nikhilmishra000/robot_arm/sw/gripper/finger2.SLDPRT

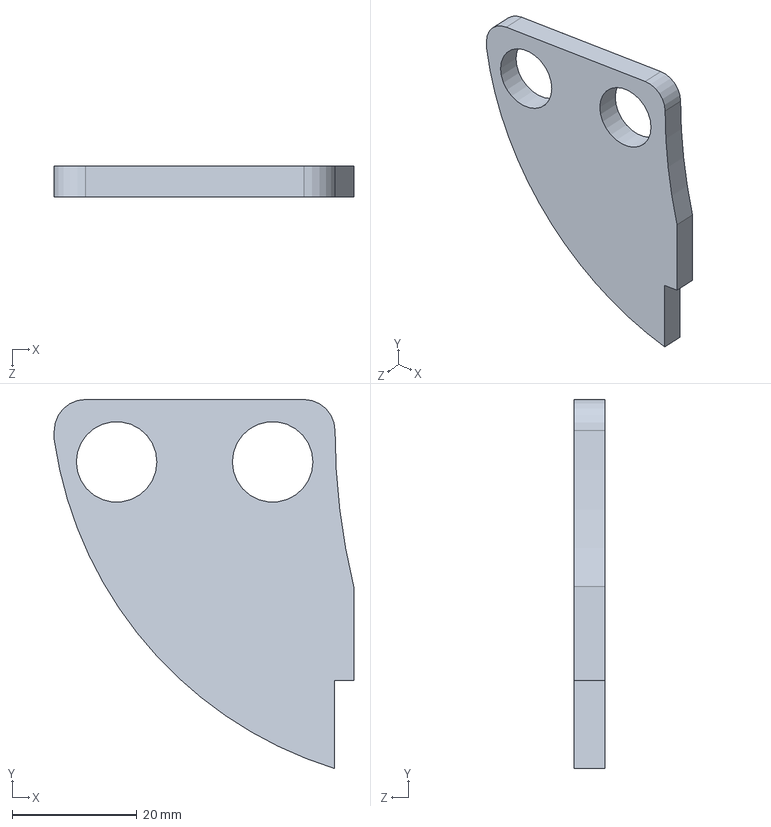
[picture p15: CAD file, 2015-05-30]
sw/gripper/finger2.SLDPRT
48.0 x 59.1 x 5.00 mm
