nikhilmishra000/robot_arm/sw/shoulder/shoulder5.SLDPRT

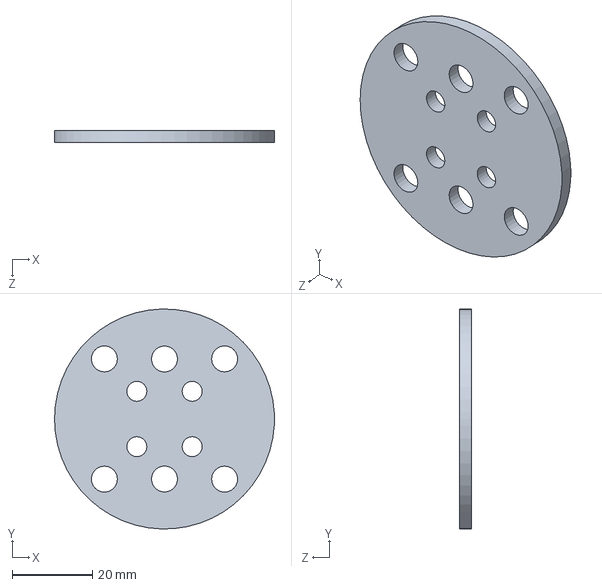
[picture p16: CAD file, 2015-05-30]
sw/shoulder/shoulder5.SLDPRT
55.0 x 55.0 x 3.10 mm
