nikhilmishra000/robot_arm/sw/upper_arm/upper_arm4.SLDPRT

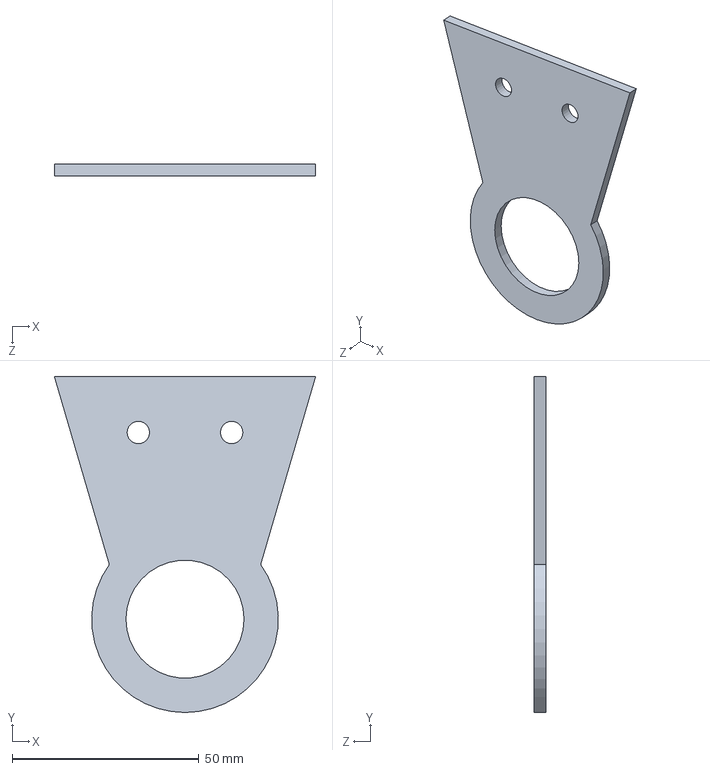
[picture p17: CAD file, 2015-05-30]
sw/upper_arm/upper_arm4.SLDPRT
70.0 x 90.0 x 3.10 mm
