nikhilmishra000/robot_arm/sw/wrist/wrist2_(1,2).SLDPRT

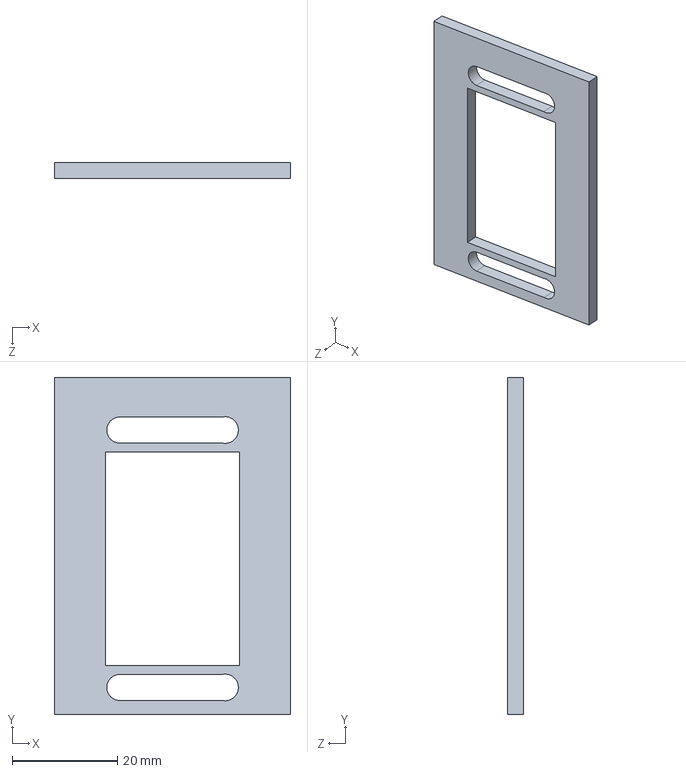
[picture p18: CAD file, 2015-05-30]
sw/wrist/wrist2_(1,2).SLDPRT
45.0 x 64.2 x 3.10 mm
