nikhilmishra000/robot_arm/sw/base/base2.SLDPRT

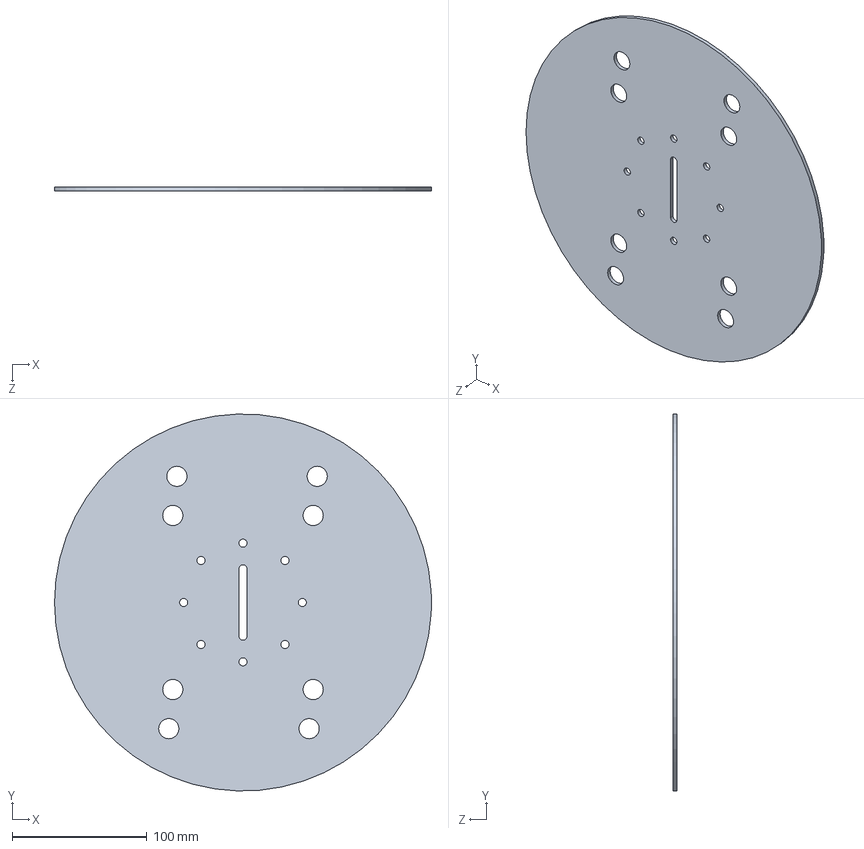
[picture p19: CAD file, 2015-05-30]
sw/base/base2.SLDPRT
279.4 x 279.3 x 3.00 mm
