nikhilmishra000/robot_arm/sw/elbow/elbow1.SLDPRT

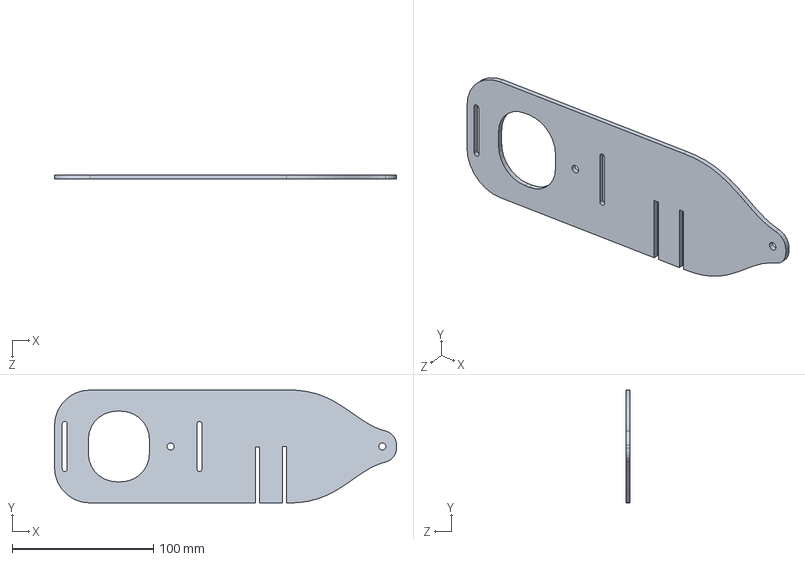
[picture p20: CAD file, 2015-05-30]
sw/elbow/elbow1.SLDPRT
242.2 x 80.0 x 3.10 mm
