nikhilmishra000/robot_arm/sw/gripper/link1.SLDPRT

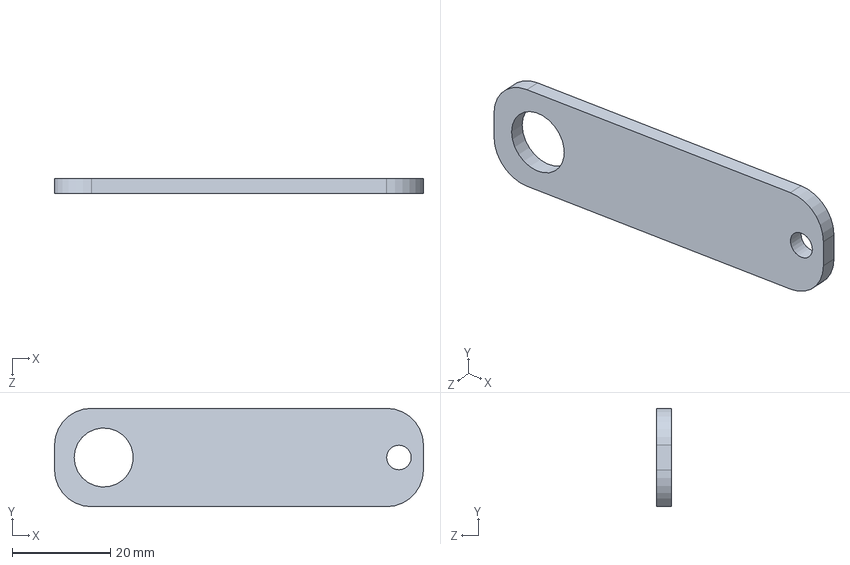
[picture p21: CAD file, 2015-05-30]
sw/gripper/link1.SLDPRT
75.0 x 20.0 x 3.10 mm
