nikhilmishra000/robot_arm/sw/shoulder/shoulder3_(1,2).SLDPRT

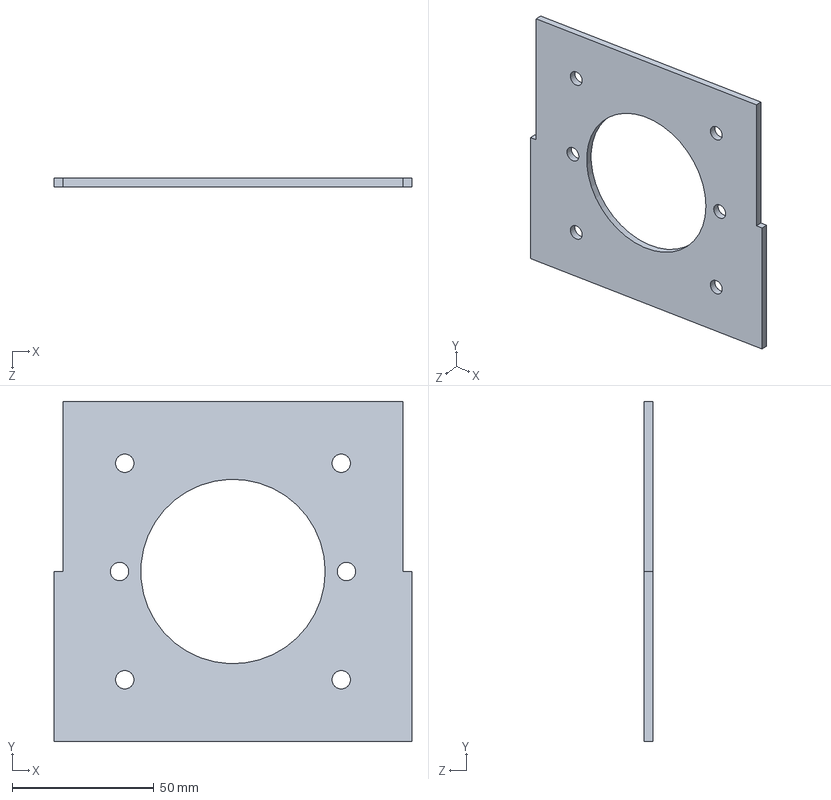
[picture p22: CAD file, 2015-05-30]
sw/shoulder/shoulder3_(1,2).SLDPRT
126.2 x 120.0 x 3.10 mm
