nikhilmishra000/robot_arm/sw/upper_arm/upper_arm3.SLDPRT

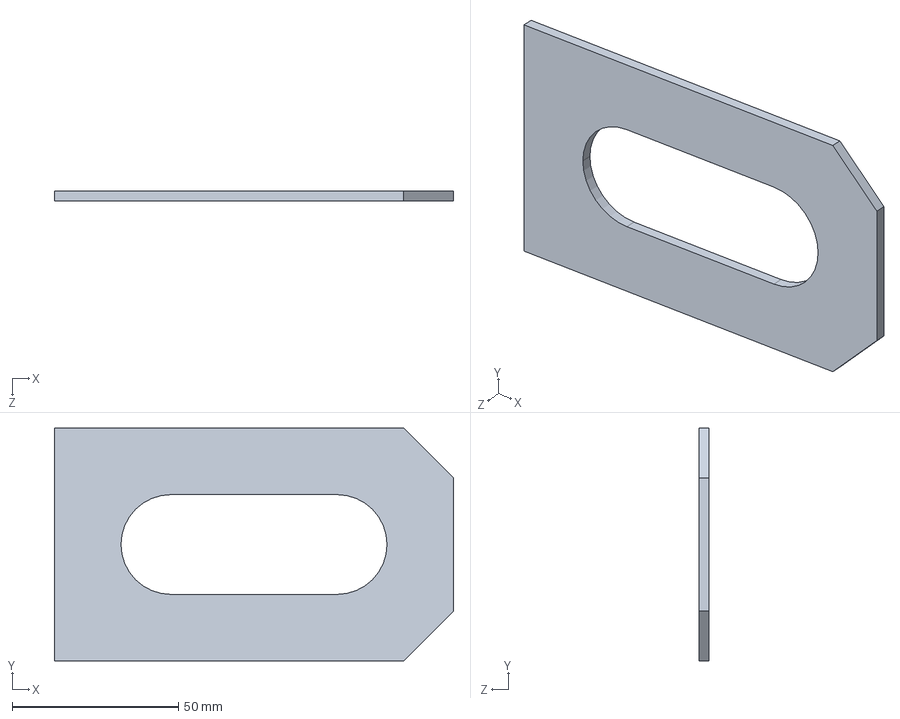
[picture p23: CAD file, 2015-05-30]
sw/upper_arm/upper_arm3.SLDPRT
120.0 x 70.0 x 3.10 mm
