nikhilmishra000/robot_arm/sw/wrist/wrist3.SLDPRT

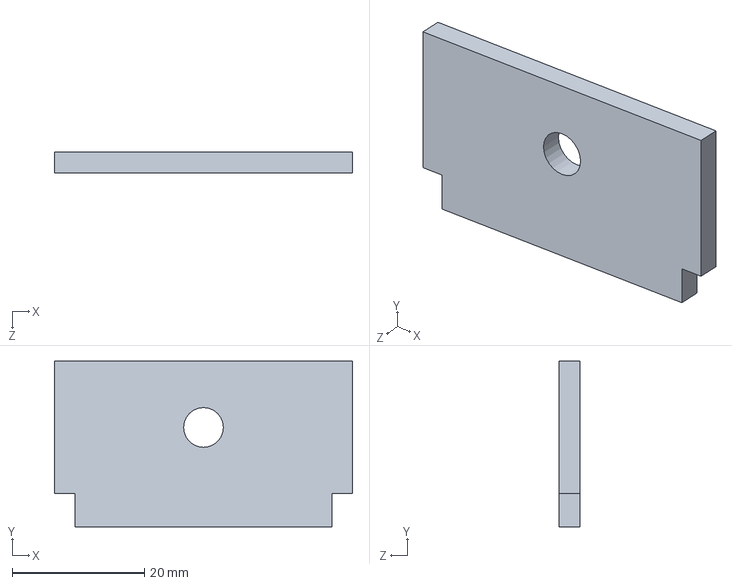
[picture p24: CAD file, 2015-05-30]
sw/wrist/wrist3.SLDPRT
45.0 x 25.0 x 3.10 mm
