nikhilmishra000/robot_arm/sw/base/base3.SLDPRT

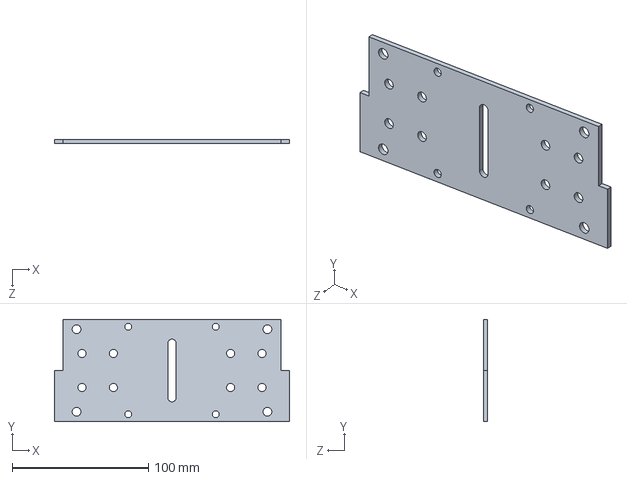
[picture p25: CAD file, 2015-05-30]
sw/base/base3.SLDPRT
172.4 x 75.0 x 3.10 mm
