nikhilmishra000/robot_arm/sw/elbow/elbow2_(1,2).SLDPRT

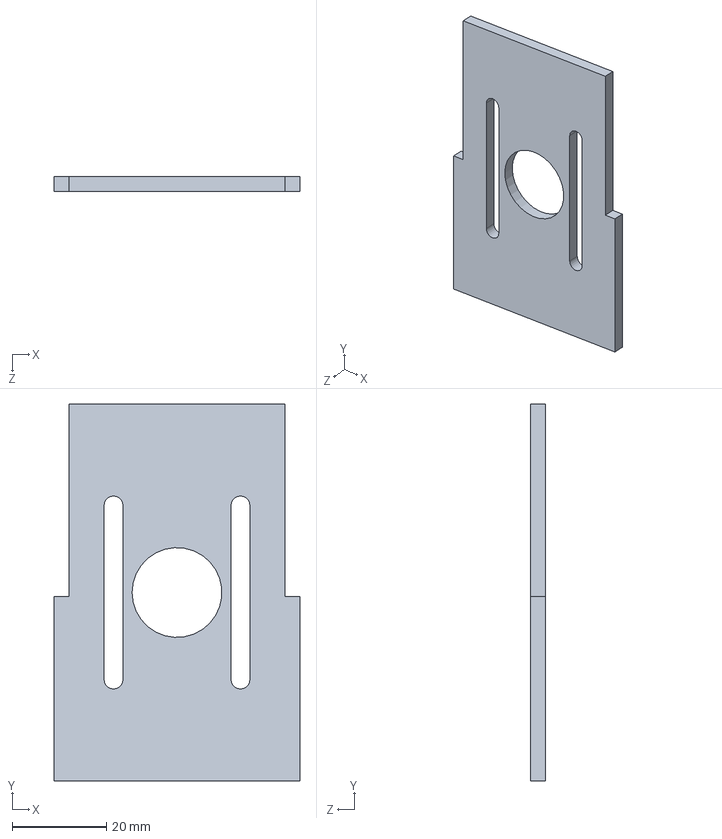
[picture p26: CAD file, 2015-05-30]
sw/elbow/elbow2_(1,2).SLDPRT
52.1 x 80.0 x 3.10 mm
