nikhilmishra000/robot_arm/sw/gripper/palm2.SLDPRT

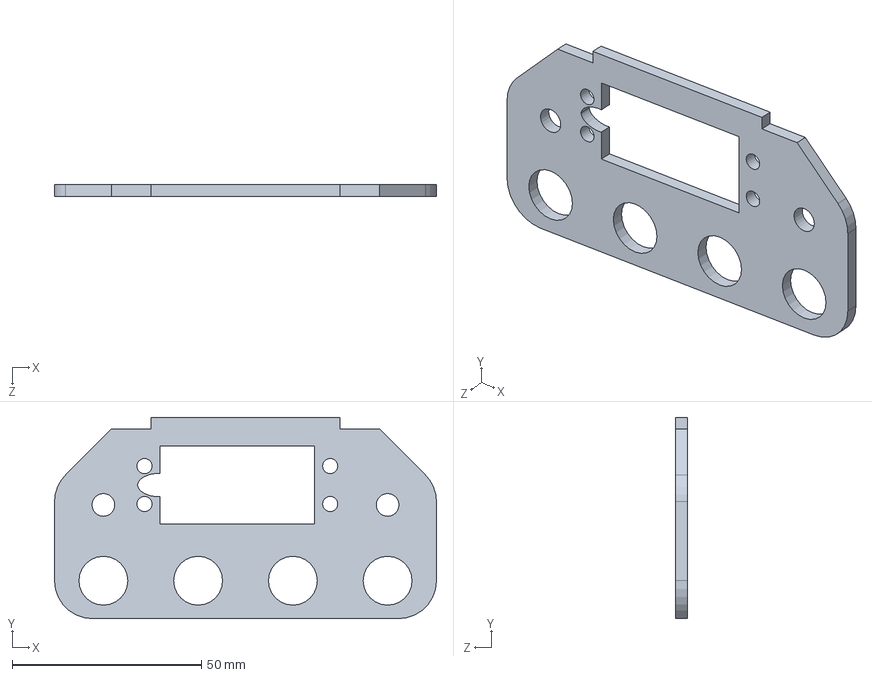
[picture p27: CAD file, 2015-05-30]
sw/gripper/palm2.SLDPRT
100.8 x 53.1 x 3.10 mm
