nikhilmishra000/robot_arm/sw/shoulder/shoulder1.SLDPRT

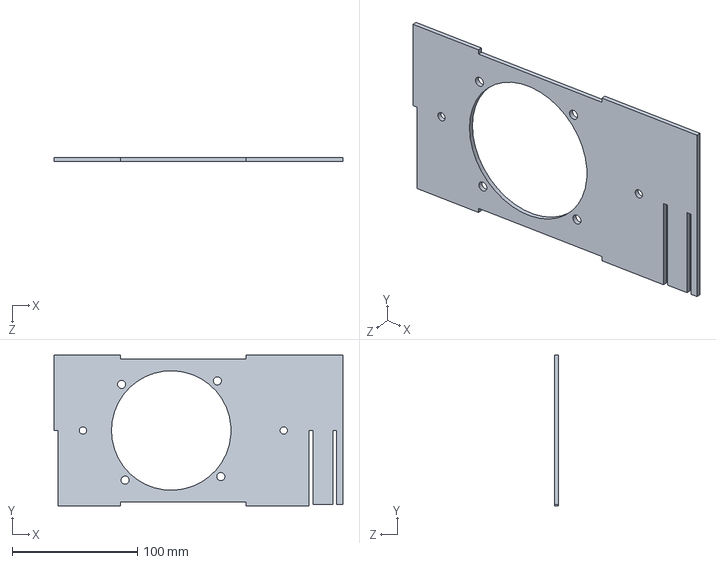
[picture p28: CAD file, 2015-05-30]
sw/shoulder/shoulder1.SLDPRT
230.3 x 120.0 x 3.10 mm
