nikhilmishra000/robot_arm/sw/upper_arm/upper_arm1.SLDPRT

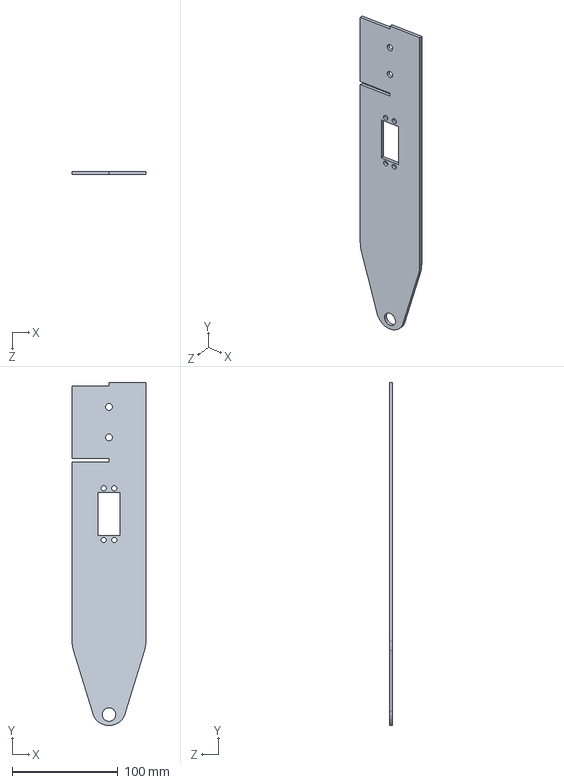
[picture p29: CAD file, 2015-05-30]
sw/upper_arm/upper_arm1.SLDPRT
70.0 x 324.5 x 3.10 mm
