nikhilmishra000/robot_arm/sw/wrist/wrist_link2.SLDPRT

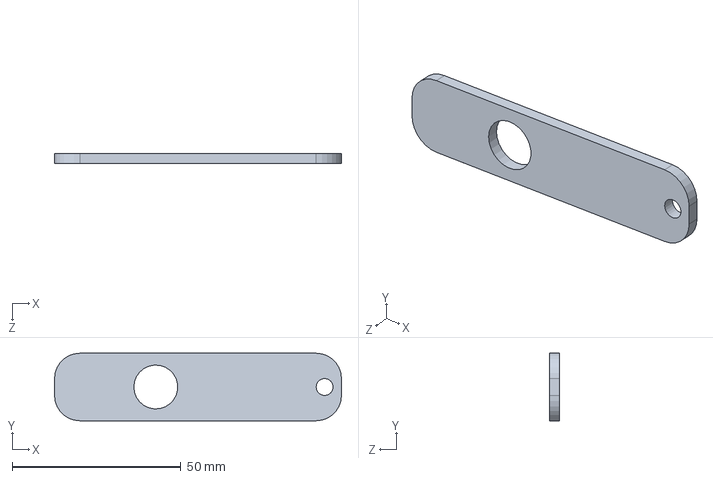
[picture p30: CAD file, 2015-05-30]
sw/wrist/wrist_link2.SLDPRT
85.0 x 20.0 x 3.10 mm
