nikhilmishra000/robot_arm/sw/base/base4.SLDPRT

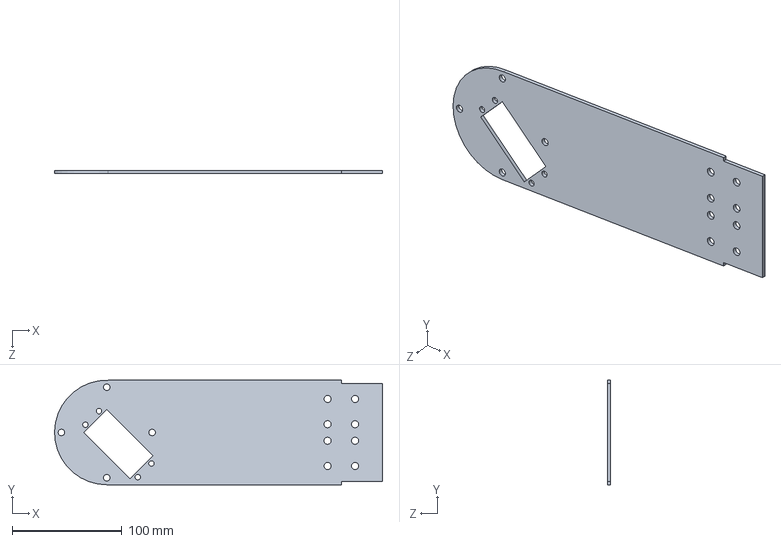
[picture p31: CAD file, 2015-05-30]
sw/base/base4.SLDPRT
298.8 x 95.2 x 3.10 mm
