nikhilmishra000/robot_arm/sw/elbow/elbow3_(1,2,3).SLDPRT

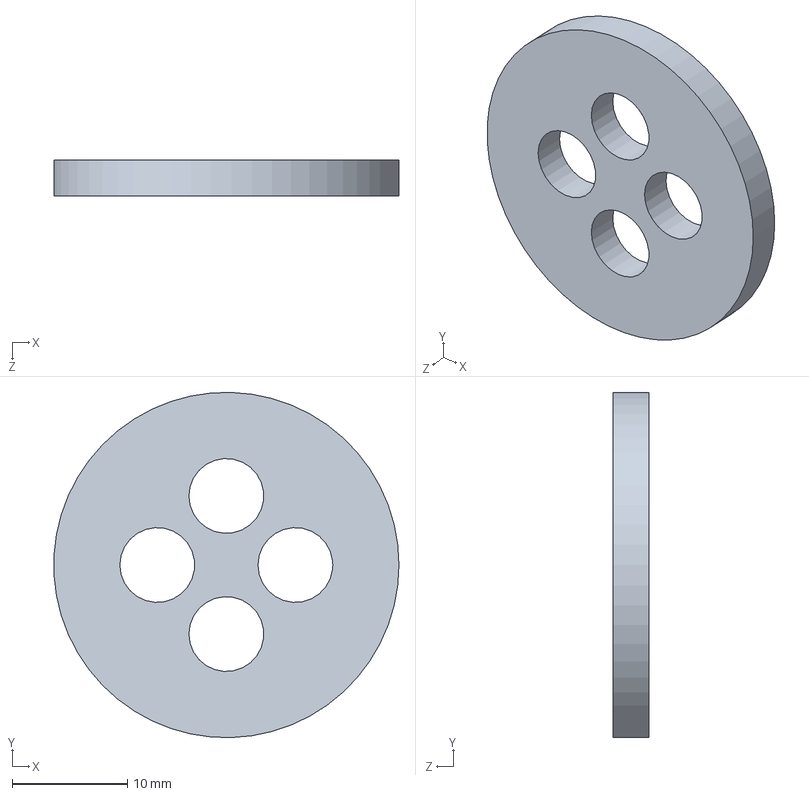
[picture p32: CAD file, 2015-05-30]
sw/elbow/elbow3_(1,2,3).SLDPRT
30.0 x 30.0 x 3.10 mm
