nikhilmishra000/robot_arm/sw/gripper/palm1.SLDPRT

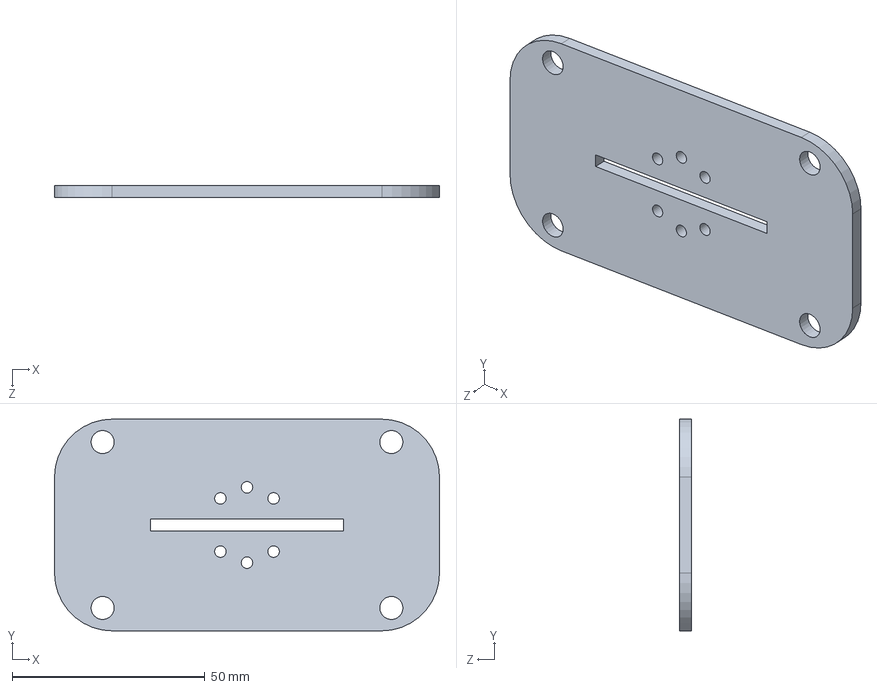
[picture p33: CAD file, 2015-05-30]
sw/gripper/palm1.SLDPRT
100.0 x 55.0 x 3.10 mm
