nikhilmishra000/robot_arm/sw/shoulder/shoulder4.SLDPRT

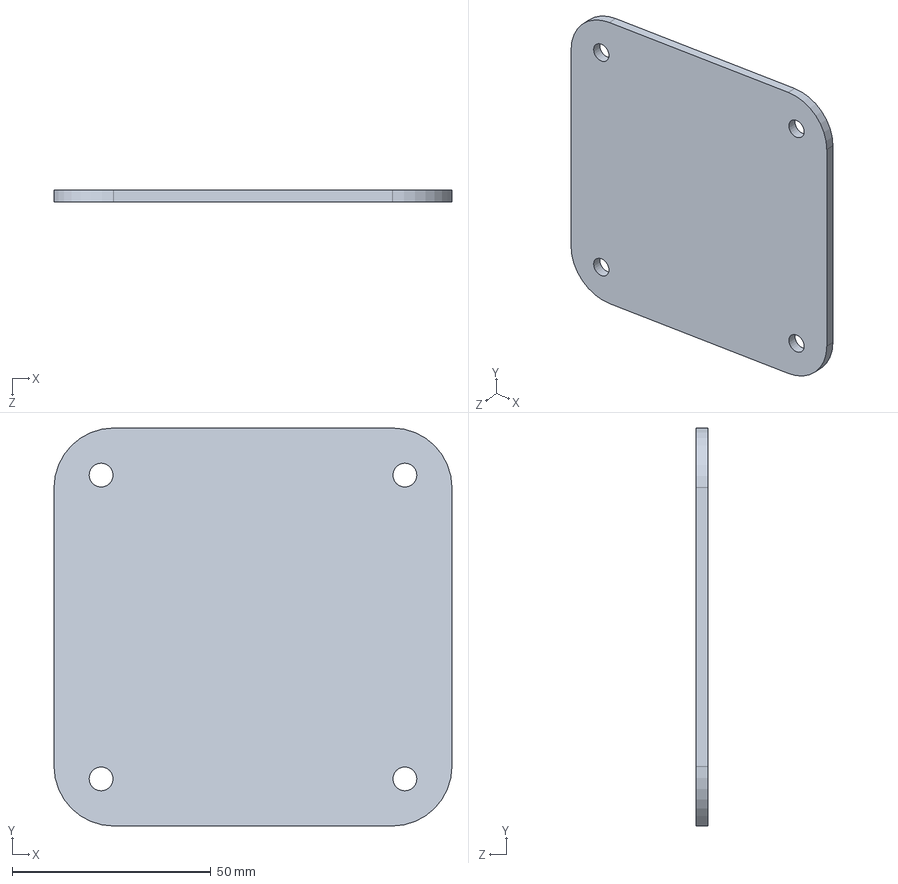
[picture p34: CAD file, 2015-05-30]
sw/shoulder/shoulder4.SLDPRT
100.0 x 100.0 x 3.10 mm
