nikhilmishra000/robot_arm/sw/wrist/wrist_link1.SLDPRT

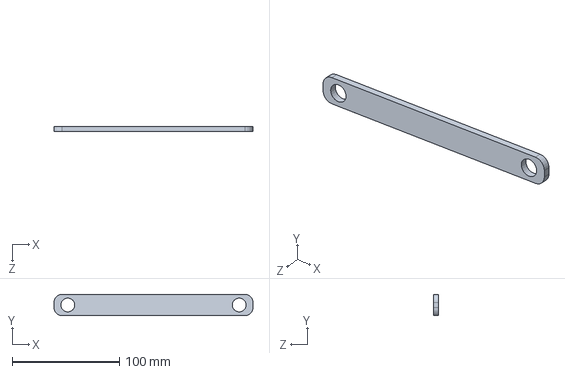
[picture p35: CAD file, 2015-05-30]
sw/wrist/wrist_link1.SLDPRT
185.8 x 20.0 x 5.00 mm
