nikhilmishra000/robot_arm/sw/gripper/link2.SLDPRT

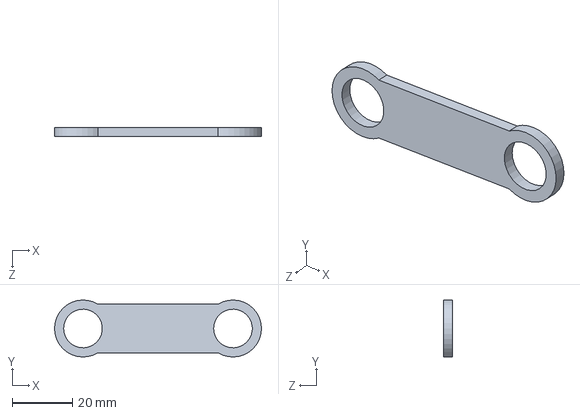
[picture p36: CAD file, 2015-05-30]
sw/gripper/link2.SLDPRT
69.0 x 19.0 x 3.10 mm
