nikhilmishra000/robot_arm/sw/gripper/finger4.SLDPRT

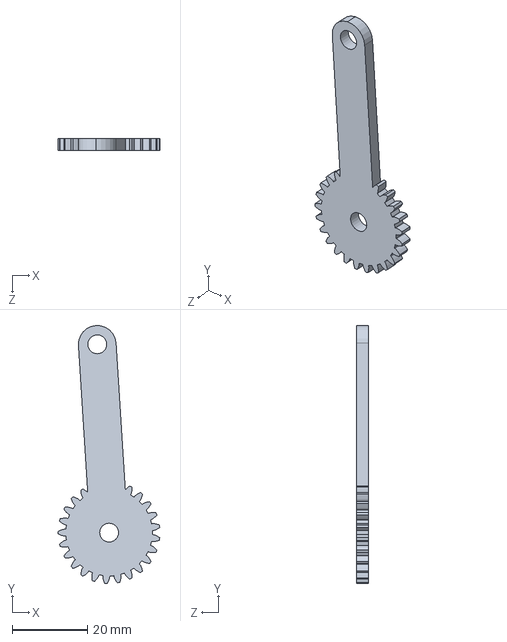
[picture p37: CAD file, 2015-05-30]
sw/gripper/finger4.SLDPRT
26.9 x 68.4 x 3.10 mm
