nikhilmishra000/robot_arm/sw/gripper/finger1.SLDPRT

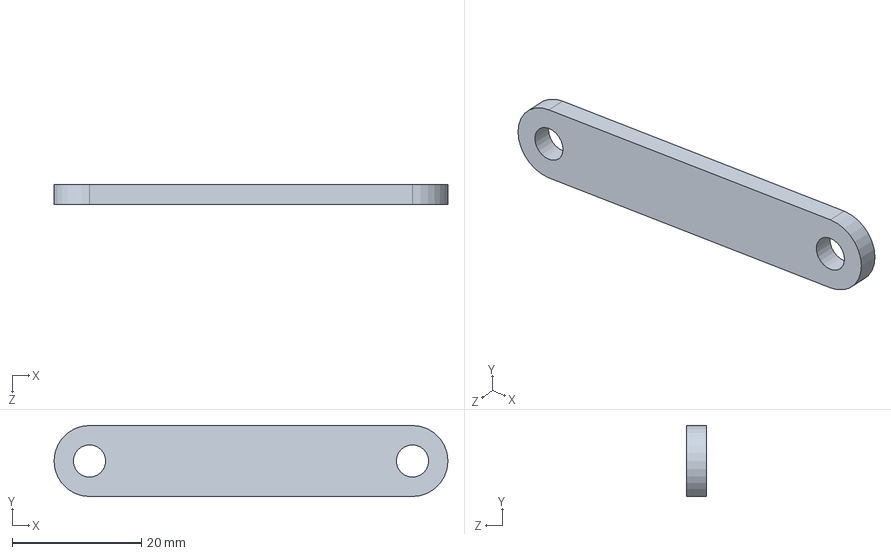
[picture p38: CAD file, 2015-05-30]
sw/gripper/finger1.SLDPRT
61.0 x 11.0 x 3.10 mm
