nikhilmishra000/robot_arm/arduino/JointLimits.h

// blue
const int GRIPPER_OPEN = 30;
const int GRIPPER_CLOSED = 95;

// green
const int WRIST_PAN_MIN = 20;
const int WRIST_PAN_MAX = 150;

// yellow, yellow
const int WRIST_ROLL_MIN = 0;
const int WRIST_ROLL_MAX = 180;

// orange
const int ELBOW_ROLL_MIN = 0;
const int ELBOW_ROLL_MAX = 180;

// blue, blue
const int ELBOW_PAN_MIN = 30;
const int ELBOW_PAN_MAX = 140;

// green
const int SHOULDER_ROLL_MIN = 0;
const int SHOULDER_ROLL_MAX = 180;

// yellow, yellow
const int SHOULDER_PAN_MIN = 60;
const int SHOULDER_PAN_MAX = 120;
